ciprian-stingu/PicIcTester/hardware/main-pcb.png

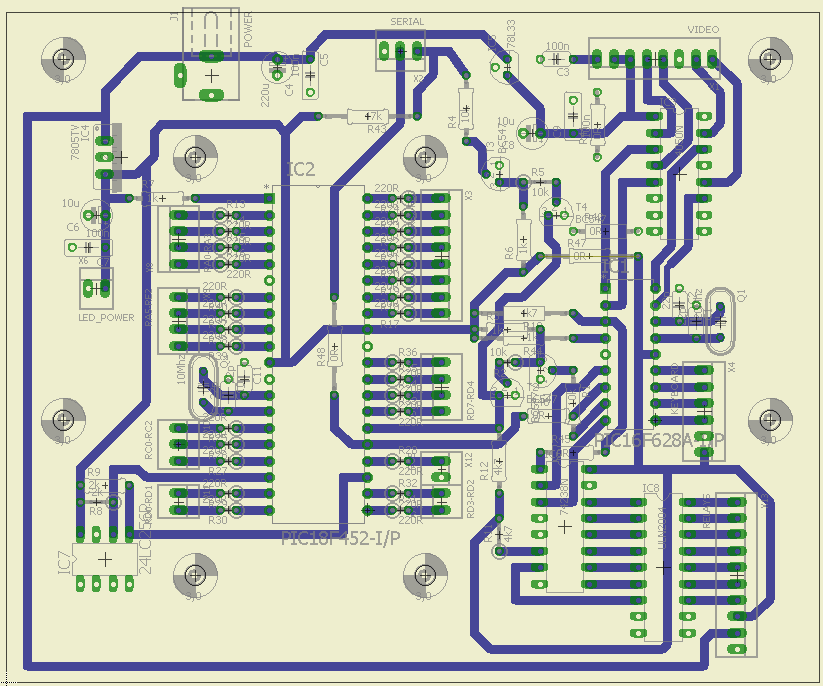
hardware/main-pcb.png
