ciprian-stingu/PicIcTester/hardware/socket-schematic.png

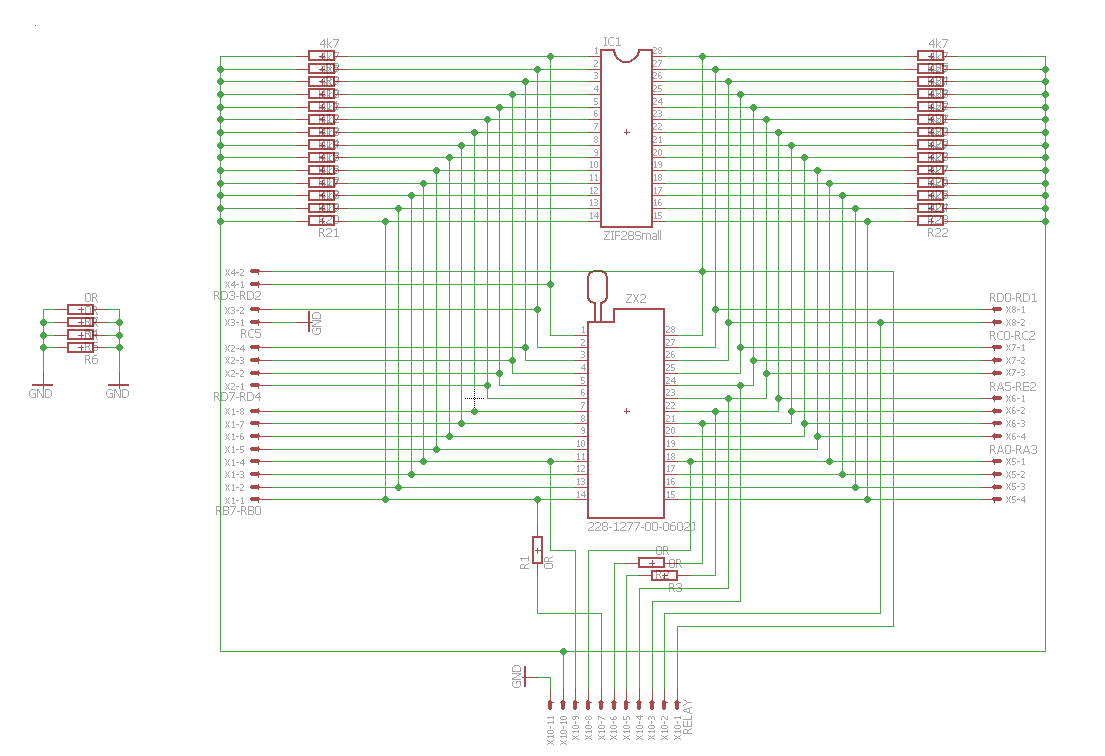
hardware/socket-schematic.png
