ciprian-stingu/PicIcTester/images/case.jpg

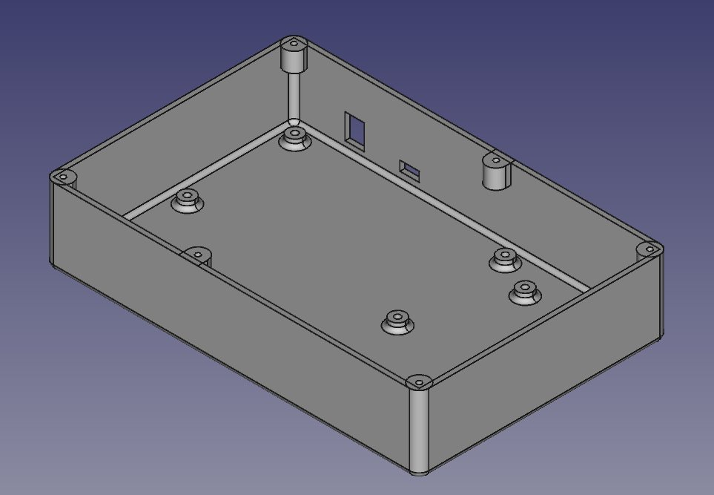
images/case.jpg
