ciprian-stingu/PicIcTester/images/face-plate.jpg

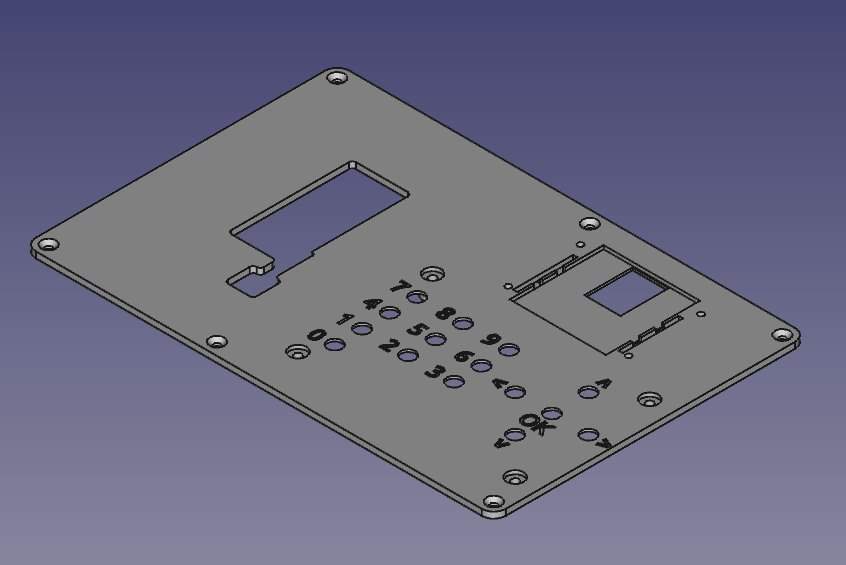
images/face-plate.jpg
