ciprian-stingu/PicIcTester/images/id-ic.jpg

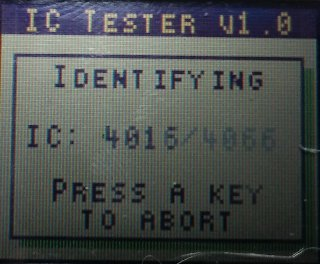
images/id-ic.jpg
