ciprian-stingu/PicIcTester/images/screen-plate.jpg

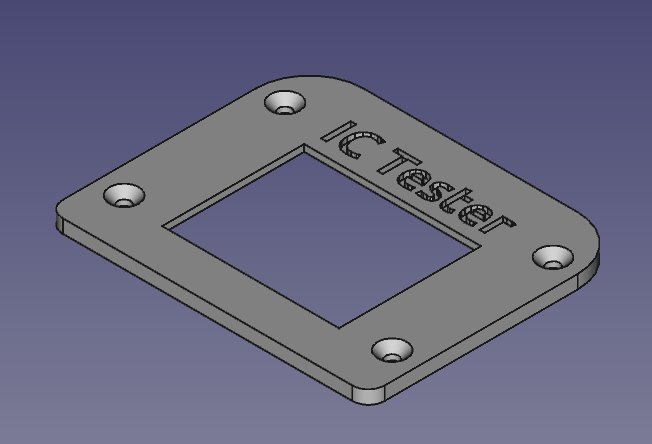
images/screen-plate.jpg
