ciprian-stingu/PicIcTester/Tester/test.c

/**
 * 
 * PicIcTester Tester
 * 
 * Copyright (C) 2020-2021 Ciprian Stingu
 * ciprian dot stingu at gmail dot com
 * 
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
 * File:   test.c
 * Author: Ciprian Stingu
 *
 * Created on July 31, 2020, 4:55 PM
 */


#include "main.h"
#include "test.h"


void ReadDatabaseInfo(void)
{
    // read test data db version
    DatabaseVersion = I2cReadDWord(EEPROM_ADDRESS, 0);
    
    //read number of devices
    TestDataDevicesCount = I2cReadDWord(EEPROM_ADDRESS, 2);
    
    //read number of tests
    TestDataRecordsCount = I2cReadDWord(EEPROM_ADDRESS, 4);
    if(TestDataRecordsCount > TEST_DATA_MAX_RECORDS) {
        TestDataRecordsCount = TEST_DATA_MAX_RECORDS;
    }
}

void SearchDeviceInEeprom(void)
{
    for(uint8_t i = 0; i < SEARCH_RESULTS; i++)
    {
        ClearString(SearchResultNames[i], SELECTED_DEVICE_NAME_MAX_LENGTH + 1);
        SearchResultIndexes[i] = TEST_DATA_INVALID_RECORD;
    }
    SearchResultsCount = 0;
    
    for(uint16_t recordIndex = 0; recordIndex < TestDataRecordsCount; recordIndex++)
    {
        uint16_t indexAddress = recordIndex * 2 + TEST_DATA_INDEX_START;
        uint16_t recordAddress = I2cReadDWord(EEPROM_ADDRESS, indexAddress);
        
        I2cReadString(EEPROM_ADDRESS, recordAddress, I2C_DATA_MAX_LENGTH, '\n');        
        
        uint8_t found = DeviceNameMatch(I2cData, SearchTerm);
        if(found != INVALID_RESULT)
        {
            for(uint8_t i = 0; i < SELECTED_DEVICE_NAME_MAX_LENGTH && I2cData[found + i] != NULL_CHAR; i++) {
                SearchResultNames[SearchResultsCount][i] = I2cData[found + i];
            }
            SearchResultIndexes[SearchResultsCount++] = recordAddress;
        }
        
        if(SearchResultsCount >= SEARCH_RESULTS) {
            break;
        }
    }
}

uint8_t TransformTestData(uint8_t *test, char *data, uint8_t pinCount)
{
    uint8_t bytesCount = pinCount / 2, realPinCount = 0;
    for(uint8_t i = 0, j = COMMON_TEST_MAX_PINS / 2; i < j; i++) {
        test[i] = 0x00;
    }

    for(uint8_t i = 0; i < bytesCount; i++)
    {
        if(*data == NULL_CHAR) {
            break;
        }
        uint8_t pin1 = GetPinFromChar(*data++);
        if(pin1 == PIN_NONE) {
            break;
        }
        realPinCount++;
        
        if(*data == NULL_CHAR) {
            break;
        }
        uint8_t pin2 = GetPinFromChar(*data++);
        if(pin2 == PIN_NONE) {
            break;
        }
        realPinCount++;
        
        test[i] = ((pin1 << 4) & 0xF0) | (pin2 & 0x0F); 
    }
    
    return realPinCount;
}

uint8_t GetPinFromChar(char data)
{
    uint8_t pin = PIN_NONE;
    
    switch(data)
    {
        case PIN_GND_CHAR:
            pin = PIN_GND;
            break;
        case PIN_VCC_CHAR:
            pin = PIN_VCC;
            break;
        case PIN_IN_LOW_CHAR:
            pin = PIN_IN_LOW;
            break;
        case PIN_IN_HIGH_CHAR:
            pin = PIN_IN_HIGH;
            break;
        case PIN_OUT_LOW_CHAR:
            pin = PIN_OUT_LOW;
            break;
        case PIN_OUT_HIGH_CHAR:
            pin = PIN_OUT_HIGH;
            break;
        case PIN_IGNORE_CHAR:
            pin = PIN_IGNORE;
            break;
        case PIN_CLOCK_CHAR:
            pin = PIN_CLOCK;
            break;
    }
    
    return pin;
}

void StartTest(uint8_t screenSource)
{
    DrawWindowOnInterface(16, 30, 66, 14, COLOR_BLUE, COLOR_WHITE, COLOR_GREEN);
    DisplayStringOnInterface(19, 34, COLOR_BLACK, COLOR_WHITE, "Testing...");
    
    TestedCases = 0;
    LastTestCaseResult = 0;
    
    uint16_t testCasesAddress = 0;
    if(screenSource == TEST_SCREEN) // load test data
    {
        uint16_t address = SelectedDeviceIndex;

        address = I2cReadString(EEPROM_ADDRESS, address, I2C_DATA_MAX_LENGTH, '\n'); //ic name
        ClearString(CommonTestName, SELECTED_DEVICE_NAME_MAX_LENGTH + 1);
        CopyString(SelectedDeviceName, CommonTestName, SELECTED_DEVICE_NAME_MAX_LENGTH);

        address = I2cReadString(EEPROM_ADDRESS, address, I2C_DATA_MAX_LENGTH, '\n'); //ignore description

        address = I2cReadString(EEPROM_ADDRESS, address, I2C_DATA_MAX_LENGTH, '\n'); //pins
        CommonTestPinCount = (I2cData[0] - '0') * 10 + (I2cData[1] - '0');
        
        testCasesAddress = address; // save test cases start address
        
        //tests count
        CommonTestCasesCount = 0;
        do
        {
            address = I2cReadString(EEPROM_ADDRESS, address, I2C_DATA_MAX_LENGTH, '\n');
            CommonTestCasesCount++;
        } while(I2cData[0] != '$' && I2cData[0] != NULL_CHAR); //no limit in test cases when reading from eeprom
    }
    
    if(CommonTestCasesCount == 0 || CommonTestPinCount == 0 || (CommonTestPinCount % 2) != 0 || CommonTestPinCount > COMMON_TEST_MAX_PINS) 
    {
        TestedCases = INVALID_RESULT;
        LastTestCaseResult = INVALID_RESULT;
        ActiveScreen = TEST_RESULT_SCREEN;
        ReturnToTestScreen = screenSource;
        ScreenChanged = TRUE;
        return;
    }
    
    if(screenSource == TEST_SCREEN) //load first test case
    {
        I2cReadString(EEPROM_ADDRESS, testCasesAddress, I2C_DATA_MAX_LENGTH, '\n');
        TransformTestData(CommonTestCases[0], I2cData, CommonTestPinCount);
    }
    
    uint8_t powerConfig = GetPowerPinsConfig(CommonTestCases[0], CommonTestPinCount);
    //set power config
    SetPowerConfig(powerConfig);

    __delay_ms(100);
    
    for(; TestedCases < CommonTestCasesCount; TestedCases++)
    {
        uint8_t *caseData;
        if(screenSource == TEST_SCREEN)
        {
            testCasesAddress = I2cReadString(EEPROM_ADDRESS, testCasesAddress, I2C_DATA_MAX_LENGTH, '\n');
            TransformTestData(CommonTestCases[0], I2cData, CommonTestPinCount);
            caseData = CommonTestCases[0];
        }
        else {
            caseData = CommonTestCases[TestedCases];
        }
        
        LastTestCaseResult = RunTestCase(caseData, CommonTestPinCount);
        if(LastTestCaseResult > 0) { // error
            break;
        }
        
        __delay_ms(50);
    }
    
    
    // disable the relays
    ResetHardware(TRUE);
    __delay_ms(100);
    
    ActiveScreen = TEST_RESULT_SCREEN;
    ReturnToTestScreen = screenSource;
    ScreenChanged = TRUE;
}

uint8_t RunTestCase(uint8_t *caseData, uint8_t pinCount)
{    
    // set ic pin function (GND/VCC/IN/OUT/CLK)
    for(uint8_t i = 0, j = pinCount / 2; i < j; i++)
    {
        PinIoOperation(IO_OP_SET_FUNCTION, (caseData[i] & 0xF0) >> 4, i * 2 + 1, pinCount);
        PinIoOperation(IO_OP_SET_FUNCTION, caseData[i] & 0x0F, i * 2 + 2, pinCount);
    }

    __delay_ms(5);

    // increment the clock if needed
    for(uint8_t i = 0, j = pinCount / 2; i < j; i++)
    {
        if((caseData[i] & 0xF0) >> 4 == PIN_CLOCK) 
        {
            PinIoOperation(IO_OP_CLOCK, 1, i * 2 + 1, pinCount);
            __delay_ms(10);
            PinIoOperation(IO_OP_CLOCK, 0, i * 2 + 1, pinCount);
        }
        if((caseData[i] & 0x0F) == PIN_CLOCK)
        {
            PinIoOperation(IO_OP_CLOCK, 1, i * 2 + 2, pinCount);
            __delay_ms(10);
            PinIoOperation(IO_OP_CLOCK, 0, i * 2 + 2, pinCount);
        }
    }

    __delay_ms(5);

    // read the ic output
    uint8_t caseResult = 0;
    
    for(uint8_t i = 0, j = pinCount / 2; i < j; i++)
    {
        uint8_t outPin = (caseData[i] & 0xF0) >> 4, result = 0;
        if(outPin == PIN_OUT_LOW)
        {
            result = PinIoOperation(IO_OP_READ_PIN, 0, i * 2 + 1, pinCount);
            if(result != 0) 
            {
                caseResult = i * 2 + 1;
                break;
            }
        }
        else if(outPin == PIN_OUT_HIGH) 
        {
            result = PinIoOperation(IO_OP_READ_PIN, 0, i * 2 + 1, pinCount);
            if(result != 1) 
            {
                caseResult = i * 2 + 1;
                break;
            }
        }

        outPin = caseData[i] & 0x0F;
        if(outPin == PIN_OUT_LOW)
        {
            result = PinIoOperation(IO_OP_READ_PIN, 0, i * 2 + 2, pinCount);
            if(result != 0) 
            {
                caseResult = i * 2 + 2;
                break;
            }
        }
        else if(outPin == PIN_OUT_HIGH) 
        {
            result = PinIoOperation(IO_OP_READ_PIN, 0, i * 2 + 2, pinCount);
            if(result != 1) 
            {
                caseResult = i * 2 + 2;
                break;
            }
        }
    }
    
    return caseResult;
}

uint8_t PinIoOperation(uint8_t type, uint8_t param, uint8_t pin, uint8_t pinCount)
{
    uint16_t configPin = pinCount << 8 | pin;
    uint8_t result = 0;
    
    switch(configPin)
    {
        case 0x1C01: // 1/28
            if(type == IO_OP_CLOCK) {
                PORTDbits.RD3 = param;
            }
            else if(type == IO_OP_READ_PIN) {
                result = PORTDbits.RD3;
            }
            else
            {
                if(param < PIN_OUT_LOW) // set as output
                {
                    TRISD3 = 0;
                    if(param < PIN_VCC) {
                        PORTDbits.RD3 = 0;
                    }
                    else {
                        PORTDbits.RD3 = 1;
                    }
                }
                else {
                    TRISD3 = 1;
                }
            } 
            break;
        case 0x1C02: // 2/28
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
                    }
                    else {
                        PORTDbits.RD2 = 1;
                    }
                }
                else {
                    TRISD2 = 1;
                }
            }
            break;
    }
    
    return result;
}

uint8_t GetPowerPinsConfig(uint8_t *test, uint8_t pinCount)
{
    switch(pinCount)
    {
        case 8:
            // 4 - GND, 8 - VCC
            break;
        case 14:
            // 7 - GND, 14 - VCC
            if(((test[3] & 0xF0) >> 4) == PIN_GND && (test[6] & 0x0F) == PIN_VCC) {
                return POWER_CONFIG_14_7_14;
            } 
            // 11 - GND, 4 - VCC
            // 10 - GND, 4 - VCC
            // 10 - GND, 5 - VCC
            break;
        case 16:
            // 8 - GND, 16 - VCC
            if((test[3] & 0x0F) == PIN_GND && (test[7] & 0x0F) == PIN_VCC) {
                return POWER_CONFIG_16_8_16;
            }
            // 12 - GND, 5 - VCC
            if((test[5] & 0x0F) == PIN_GND && ((test[2] & 0xF0) >> 4) == PIN_VCC) {
                return POWER_CONFIG_16_12_5;
            }
            // 13 - GND, 5 - VCC
            break;
        case 18:
            // 9 - GND, 18 - VCC
            if(((test[4] & 0xF0) >> 4) == PIN_GND && (test[8] & 0x0F) == PIN_VCC) {
                return POWER_CONFIG_18_9_18;
            }
            break;
        case 20:
            // 10 - GND, 20 - VCC
            if((test[4] & 0x0F) == PIN_GND && (test[9] & 0x0F) == PIN_VCC) {
                return POWER_CONFIG_20_10_20;
            }
            break;
        case 24:
            // 12 - GND, 24 - VCC
            if((test[5] & 0x0F) == PIN_GND && (test[11] & 0x0F) == PIN_VCC) {
                return POWER_CONFIG_24_12_24;
            }
            break;
        case 28:
            // 14 - GND, 28 - VCC
            if((test[6] & 0x0F) == PIN_GND && (test[13] & 0x0F) == PIN_VCC) {
                return POWER_CONFIG_28_14_28;
            }
            break;
    }
    
    return POWER_CONFIG_UNKNOWN;
}

void SetPowerConfig(uint8_t powerConfig)
{
    UartWriteString("_R ");

    char hexBuffer[3];
    ByteToAsciiHex(powerConfig, hexBuffer);
    UartWriteString(hexBuffer);

    InterfaceCmdStatus = INTERFACE_CMD_READY;
    UartWriteString("\n");        
    while(InterfaceCmdStatus != INTERFACE_CMD_DONE) {
        __delay_us(25);
    }
}

void ResetHardware(uint8_t fullReset)
{
    if(fullReset) {
        SetPowerConfig(POWER_CONFIG_UNKNOWN);
    }
    
    for(uint8_t i = 0, j = COMMON_TEST_MAX_PINS / 2; i < j; i++)
    {
        PinIoOperation(IO_OP_SET_FUNCTION, PIN_IN_LOW, i * 2 + 1, COMMON_TEST_MAX_PINS);
        PinIoOperation(IO_OP_SET_FUNCTION, PIN_IN_LOW, i * 2 + 2, COMMON_TEST_MAX_PINS);
    }
}

uint8_t IdentifyIcTest(uint16_t index, uint8_t pinCount, char *deviceName)
{
    uint16_t indexAddress = index * 2 + TEST_DATA_INDEX_START;
    uint16_t icTestAddress = I2cReadDWord(EEPROM_ADDRESS, indexAddress);
    
    icTestAddress = I2cReadString(EEPROM_ADDRESS, icTestAddress, I2C_DATA_MAX_LENGTH, '\n'); //ic name
    char icTestDeviceName[10];
    ClearString(icTestDeviceName, 10);
    CopyString(&I2cData[1], icTestDeviceName, 9);

    icTestAddress = I2cReadString(EEPROM_ADDRESS, icTestAddress, I2C_DATA_MAX_LENGTH, '\n'); //ignore description

    icTestAddress = I2cReadString(EEPROM_ADDRESS, icTestAddress, I2C_DATA_MAX_LENGTH, '\n'); //pins
    uint8_t icTestPinCount = (I2cData[0] - '0') * 10 + (I2cData[1] - '0');
    if(icTestPinCount != pinCount) { // pins don't match
        return INVALID_RESULT;
    }
    
    ClearRectangleOnInterface(32, 32, 54, 6, COLOR_WHITE); // clear previous ic name...
    DisplayStringOnInterface(32, 32, COLOR_BLACK, COLOR_WHITE, icTestDeviceName);
    
    ResetHardware(FALSE);
    __delay_ms(50);
    
    uint8_t icTestCase[COMMON_TEST_MAX_PINS / 2], icTestCaseResult = 0;
    
    while(TRUE)
    {
        icTestAddress = I2cReadString(EEPROM_ADDRESS, icTestAddress, I2C_DATA_MAX_LENGTH, '\n');
        if(I2cData[0] == '$' || I2cData[0] == NULL_CHAR) {
            break;
        }
        
        TransformTestData(icTestCase, I2cData, icTestPinCount);
        
        icTestCaseResult = RunTestCase(icTestCase, icTestPinCount);
        if(icTestCaseResult > 0) { // error
            break;
        }
        
        __delay_ms(10);
    }
    
    if(icTestCaseResult == 0) 
    {
        CopyString(icTestDeviceName, deviceName, 9);
        return 0;
    }
    return INVALID_RESULT;
}

#ifdef HARDWARE_DEBUG

void HwDebugSetOutAllLow(void)
{
    for(uint8_t i = 0, j = COMMON_TEST_MAX_PINS / 2; i < j; i++)
    {
        PinIoOperation(IO_OP_SET_FUNCTION, PIN_IN_LOW, i * 2 + 1, COMMON_TEST_MAX_PINS);
        PinIoOperation(IO_OP_SET_FUNCTION, PIN_IN_LOW, i * 2 + 2, COMMON_TEST_MAX_PINS);
    }
}

void HwDebugSetOutAllHigh(void)
{
    for(uint8_t i = 0, j = COMMON_TEST_MAX_PINS / 2; i < j; i++)
    {
        PinIoOperation(IO_OP_SET_FUNCTION, PIN_IN_HIGH, i * 2 + 1, COMMON_TEST_MAX_PINS);
        PinIoOperation(IO_OP_SET_FUNCTION, PIN_IN_HIGH, i * 2 + 2, COMMON_TEST_MAX_PINS);
    }
}

void HwDebugSetOutAllHL(void)
{
    for(uint8_t i = 0, j = COMMON_TEST_MAX_PINS / 2; i < j; i++)
    {
        PinIoOperation(IO_OP_SET_FUNCTION, PIN_IN_HIGH, i * 2 + 1, COMMON_TEST_MAX_PINS);
        PinIoOperation(IO_OP_SET_FUNCTION, PIN_IN_LOW, i * 2 + 2, COMMON_TEST_MAX_PINS);
    }
}

void HwDebugSetOutAllLH(void)
{
    for(uint8_t i = 0, j = COMMON_TEST_MAX_PINS / 2; i < j; i++)
    {
        PinIoOperation(IO_OP_SET_FUNCTION, PIN_IN_LOW, i * 2 + 1, COMMON_TEST_MAX_PINS);
        PinIoOperation(IO_OP_SET_FUNCTION, PIN_IN_HIGH, i * 2 + 2, COMMON_TEST_MAX_PINS);
    }
}

void HwDebugRelay1(void)
{
    SetPowerConfig(POWER_CONFIG_UNKNOWN);
    
    HwDebugSetOutAllLow();
    // 7 - GND, 14 - VCC
    SetPowerConfig(POWER_CONFIG_14_7_14);
    PinIoOperation(IO_OP_SET_FUNCTION, PIN_GND, 7, 14);
    PinIoOperation(IO_OP_SET_FUNCTION, PIN_VCC, 14, 14);
}

void HwDebugRelay2(void)
{
    SetPowerConfig(POWER_CONFIG_UNKNOWN);
    
    HwDebugSetOutAllLow();
    // 8 - GND, 16 - VCC
    SetPowerConfig(POWER_CONFIG_16_8_16);
    PinIoOperation(IO_OP_SET_FUNCTION, PIN_GND, 8, 16);
    PinIoOperation(IO_OP_SET_FUNCTION, PIN_VCC, 16, 16);
}

void HwDebugRelay3(void)
{
    SetPowerConfig(POWER_CONFIG_UNKNOWN);
    
    HwDebugSetOutAllLow();
    // 9 - GND, 18 - VCC
    SetPowerConfig(POWER_CONFIG_18_9_18);
    PinIoOperation(IO_OP_SET_FUNCTION, PIN_GND, 9, 18);
    PinIoOperation(IO_OP_SET_FUNCTION, PIN_VCC, 18, 18);
}

void HwDebugRelay4(void)
{
    SetPowerConfig(POWER_CONFIG_UNKNOWN);
    
    HwDebugSetOutAllLow();
    // 12 - GND, 5 - VCC
    SetPowerConfig(POWER_CONFIG_16_12_5);
    PinIoOperation(IO_OP_SET_FUNCTION, PIN_GND, 12, 16);
    PinIoOperation(IO_OP_SET_FUNCTION, PIN_VCC, 5, 16);
}

void HwDebugRelay5(void)
{
    SetPowerConfig(POWER_CONFIG_UNKNOWN);
    
    HwDebugSetOutAllLow();
    // 10 - GND, 20 - VCC
    SetPowerConfig(POWER_CONFIG_20_10_20);
    PinIoOperation(IO_OP_SET_FUNCTION, PIN_GND, 10, 20);
    PinIoOperation(IO_OP_SET_FUNCTION, PIN_VCC, 20, 20);
}

void HwDebugRelay6(void)
{
    SetPowerConfig(POWER_CONFIG_UNKNOWN);
    
    HwDebugSetOutAllLow();
    // 12 - GND, 24 - VCC
    SetPowerConfig(POWER_CONFIG_24_12_24);
    PinIoOperation(IO_OP_SET_FUNCTION, PIN_GND, 12, 24);
    PinIoOperation(IO_OP_SET_FUNCTION, PIN_VCC, 24, 24);
}

void HwDebugRelay7(void)
{
    SetPowerConfig(POWER_CONFIG_UNKNOWN);
    
    HwDebugSetOutAllLow();
    // 14 - GND, 28 - VCC
    SetPowerConfig(POWER_CONFIG_28_14_28);
    PinIoOperation(IO_OP_SET_FUNCTION, PIN_GND, 14, 28);
    PinIoOperation(IO_OP_SET_FUNCTION, PIN_VCC, 28, 28);
}

#endif
